mirzafahad/halloween_mask/code/Uncanny_Eyes/convert/catEye/lid-lower-symmetrical.png

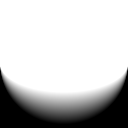
code/Uncanny_Eyes/convert/catEye/lid-lower-symmetrical.png
