mirzafahad/halloween_mask/code/Uncanny_Eyes/convert/catEye/lid-lower.png

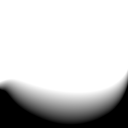
code/Uncanny_Eyes/convert/catEye/lid-lower.png
