mirzafahad/halloween_mask/code/Uncanny_Eyes/convert/catEye/lid-upper-symmetrical.png

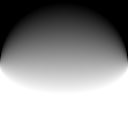
code/Uncanny_Eyes/convert/catEye/lid-upper-symmetrical.png
