mirzafahad/halloween_mask/code/Uncanny_Eyes/convert/catEye/lid-upper.png

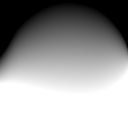
code/Uncanny_Eyes/convert/catEye/lid-upper.png
