mirzafahad/halloween_mask/code/Uncanny_Eyes/convert/catEye/pupilMap.png

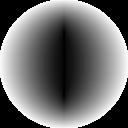
code/Uncanny_Eyes/convert/catEye/pupilMap.png
