mirzafahad/halloween_mask/code/Uncanny_Eyes/convert/catEye/sclera.png

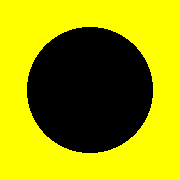
code/Uncanny_Eyes/convert/catEye/sclera.png
