mirzafahad/halloween_mask/code/Uncanny_Eyes/convert/defaultEye/lid-lower.png

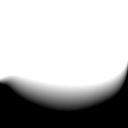
code/Uncanny_Eyes/convert/defaultEye/lid-lower.png
