mirzafahad/halloween_mask/code/Uncanny_Eyes/convert/defaultEye/sclera.png

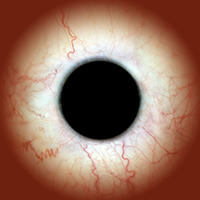
code/Uncanny_Eyes/convert/defaultEye/sclera.png
