mirzafahad/halloween_mask/code/Uncanny_Eyes/convert/doeEye/sclera.png

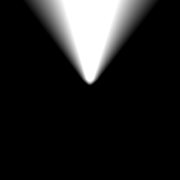
code/Uncanny_Eyes/convert/doeEye/sclera.png
