mirzafahad/halloween_mask/code/Uncanny_Eyes/convert/dragonEye/pupilMap.png

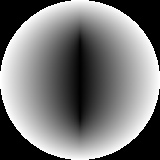
code/Uncanny_Eyes/convert/dragonEye/pupilMap.png
