mirzafahad/halloween_mask/code/Uncanny_Eyes/convert/goatEye/pupilMap.png

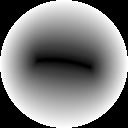
code/Uncanny_Eyes/convert/goatEye/pupilMap.png
