mirzafahad/halloween_mask/code/Uncanny_Eyes/convert/naugaEye/sclera.png

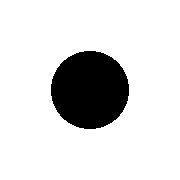
code/Uncanny_Eyes/convert/naugaEye/sclera.png
