mirzafahad/halloween_mask/code/Uncanny_Eyes/convert/newtEye/sclera.png

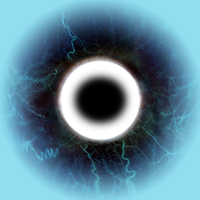
code/Uncanny_Eyes/convert/newtEye/sclera.png
