mirzafahad/halloween_mask/code/Uncanny_Eyes/convert/terminatorEye/lid-upper-symmetrical.png

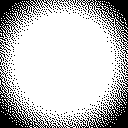
code/Uncanny_Eyes/convert/terminatorEye/lid-upper-symmetrical.png
