mirzafahad/halloween_mask/code/Uncanny_Eyes/convert/terminatorEye/sclera.png

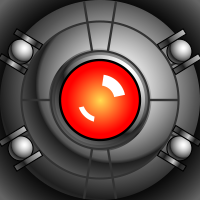
code/Uncanny_Eyes/convert/terminatorEye/sclera.png
